johanndiedrick/nakedear/presentation/img/amplifier.png

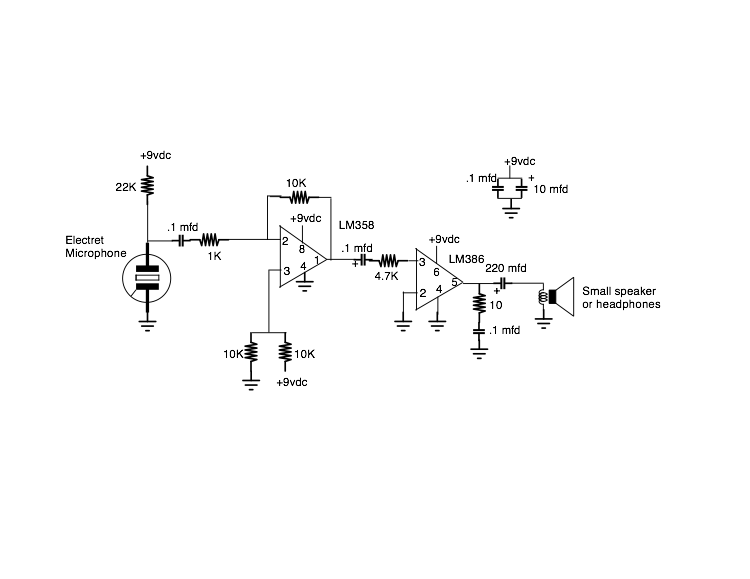
presentation/img/amplifier.png
