johanndiedrick/nakedear/presentation/img/estonia3.jpg

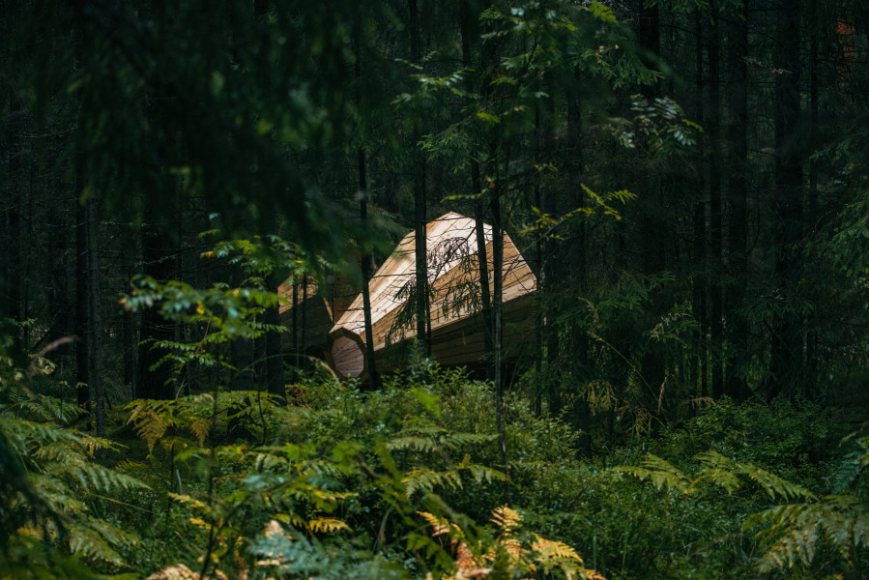
presentation/img/estonia3.jpg
