johanndiedrick/nakedear/presentation/img/hairhymn.png

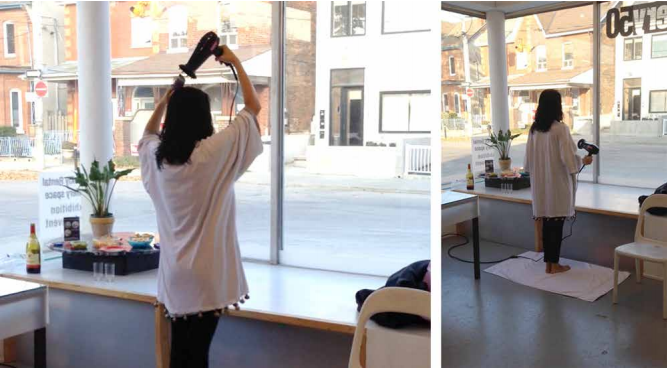
presentation/img/hairhymn.png
