johanndiedrick/nakedear/presentation/img/humanhearing.jpeg

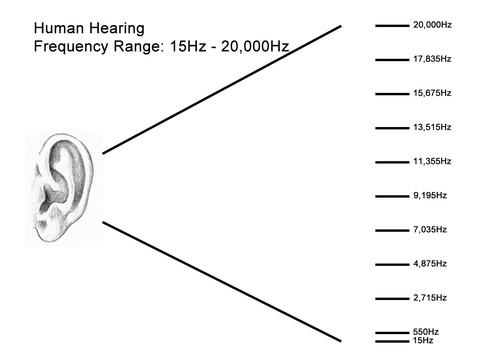
presentation/img/humanhearing.jpeg
