johanndiedrick/nakedear/presentation/img/loudspeaker.png

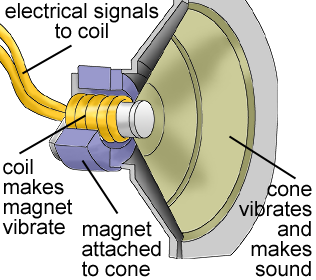
presentation/img/loudspeaker.png
