johanndiedrick/nakedear/presentation/img/microphonework.jpg

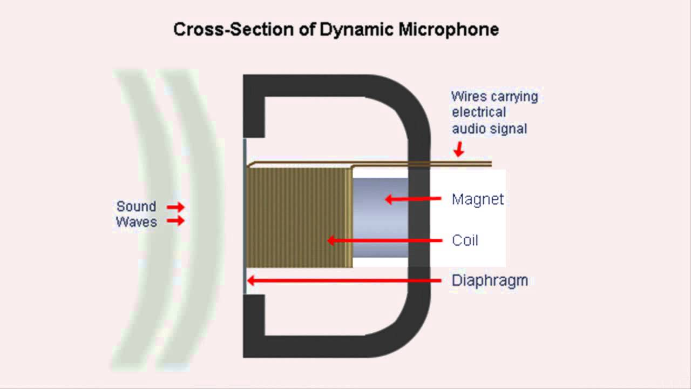
presentation/img/microphonework.jpg
