johanndiedrick/nakedear/presentation/img/punk.jpg

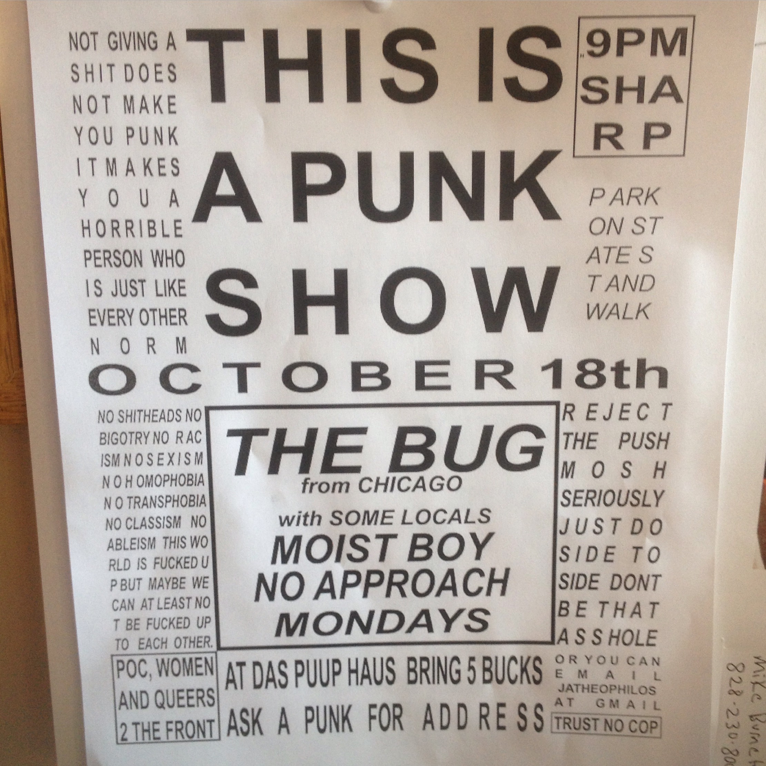
presentation/img/punk.jpg
