johanndiedrick/nakedear/materials/boxes/references/069354-1-01.jpg

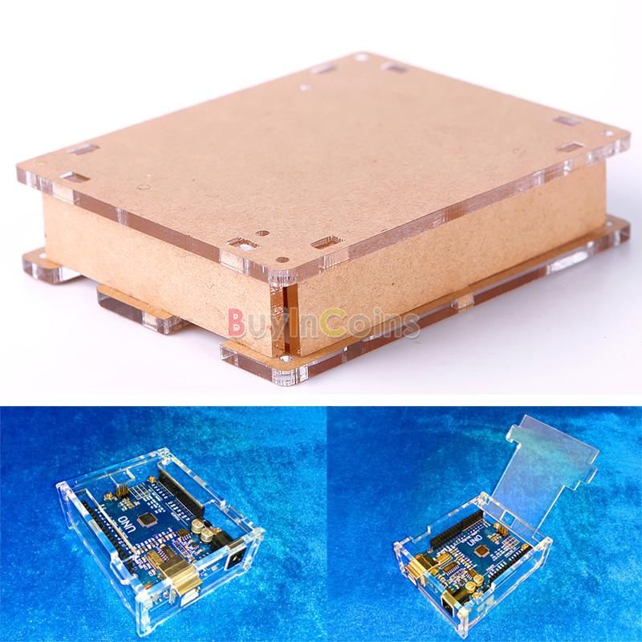
materials/boxes/references/069354-1-01.jpg
