johanndiedrick/nakedear/materials/boxes/references/069354-1-03.jpg

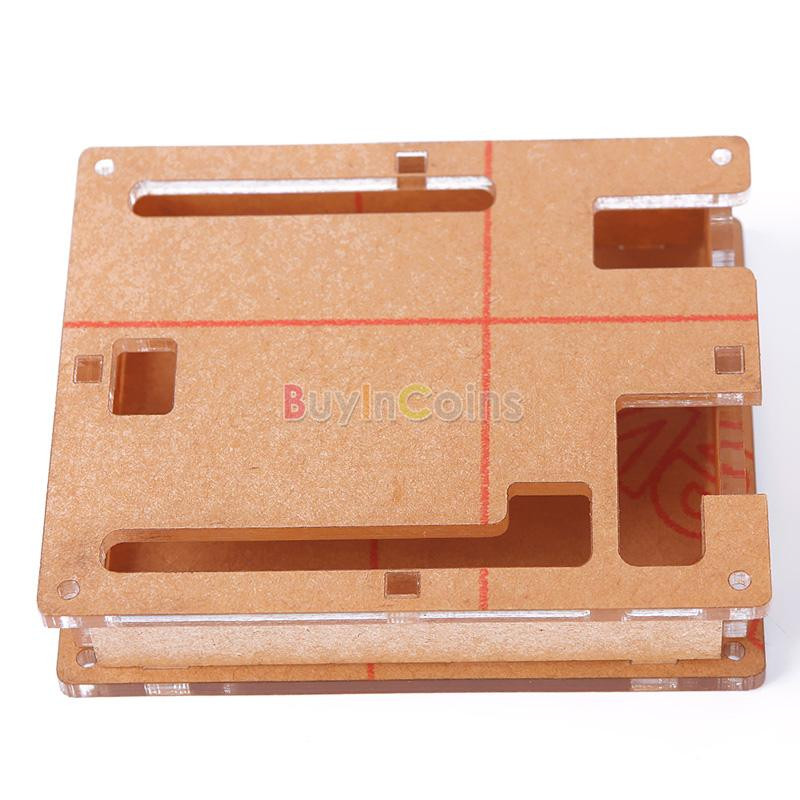
materials/boxes/references/069354-1-03.jpg
