johanndiedrick/nakedear/materials/boxes/references/069354-1-04.jpg

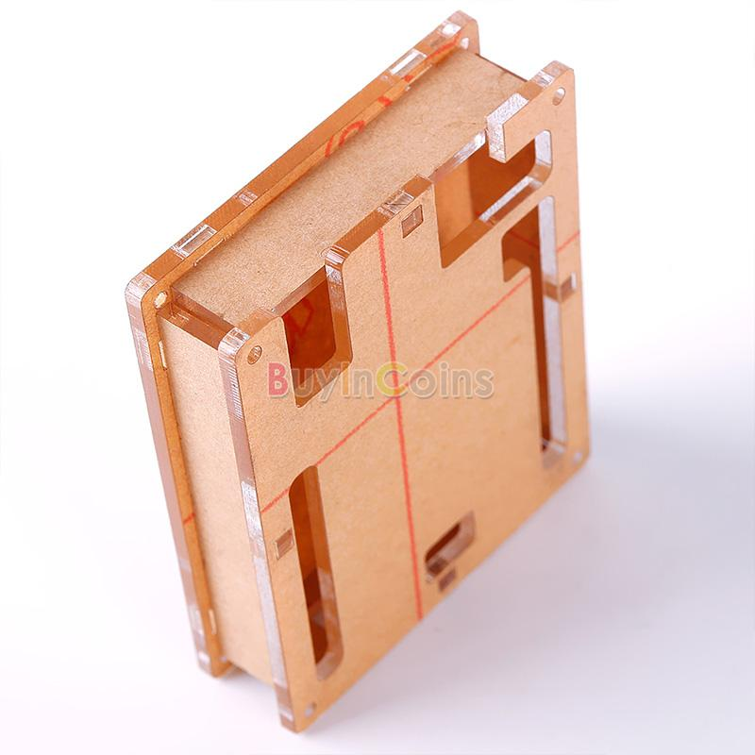
materials/boxes/references/069354-1-04.jpg
