johanndiedrick/nakedear/materials/boxes/references/069354-1-05.jpg

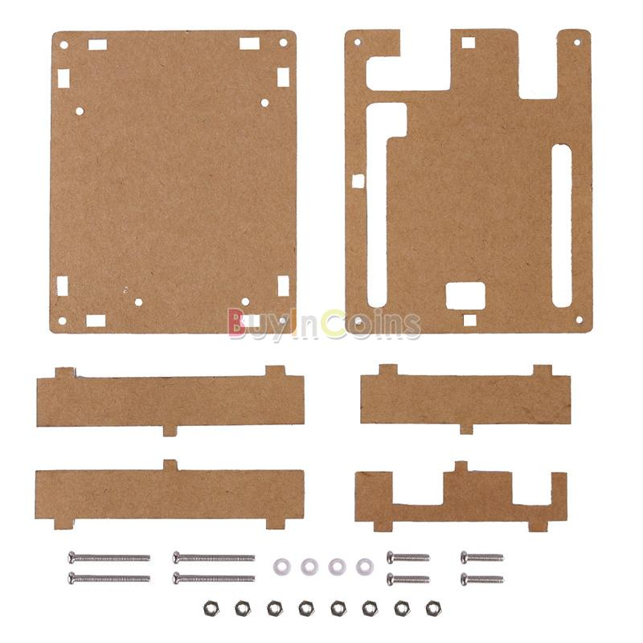
materials/boxes/references/069354-1-05.jpg
